drmoratorius/steampack/docs/pics/steampack-01.jpg

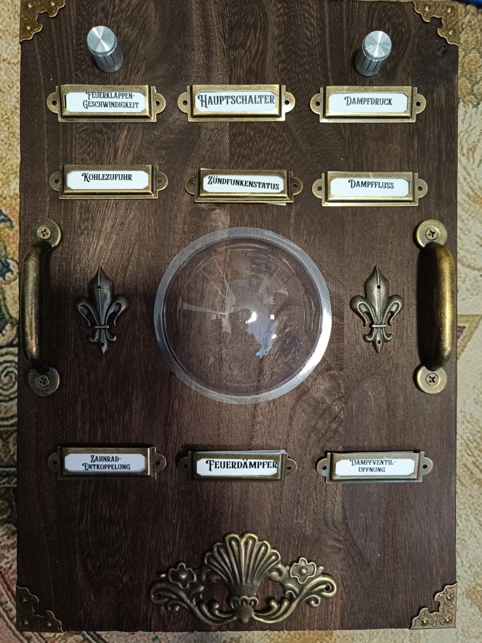
docs/pics/steampack-01.jpg
