drmoratorius/steampack/docs/pics/steampack-02.jpg

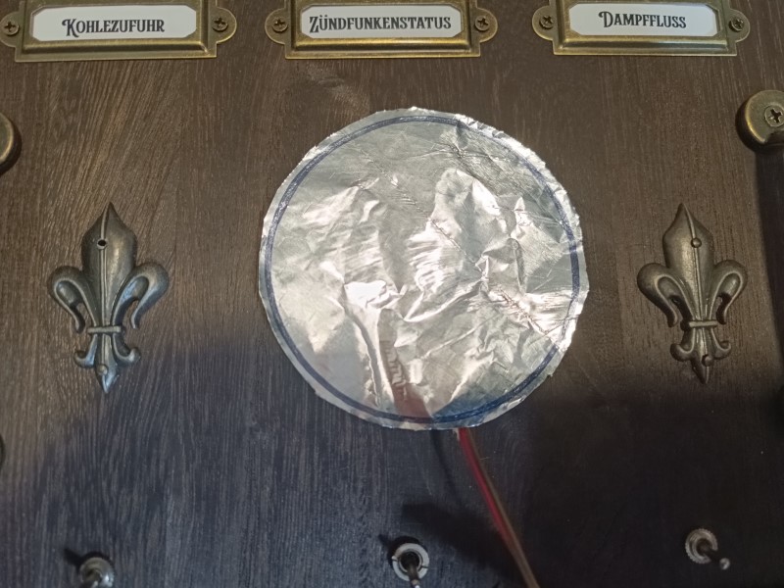
docs/pics/steampack-02.jpg
