drmoratorius/steampack/docs/pics/steampack-13.jpg

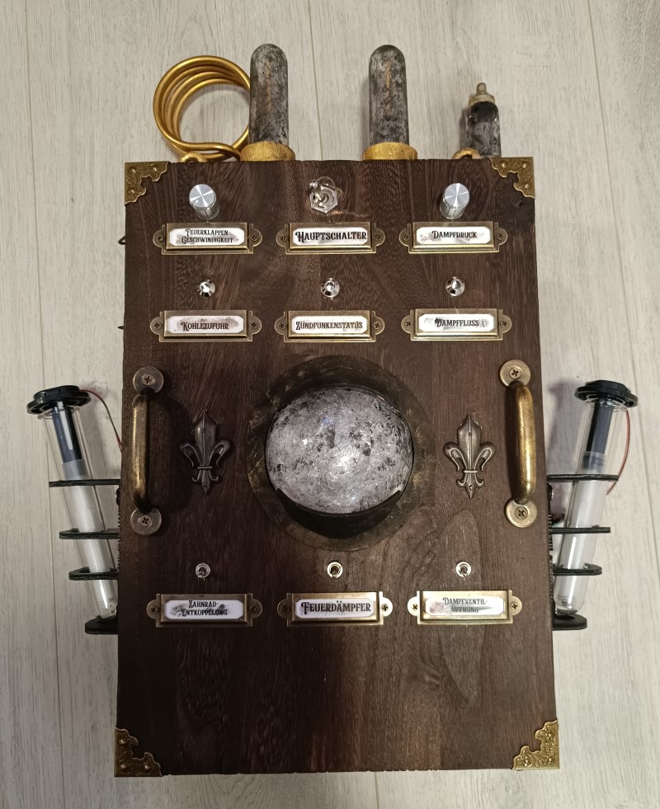
docs/pics/steampack-13.jpg
