drmoratorius/steampack/docs/pics/steampack-15.jpg

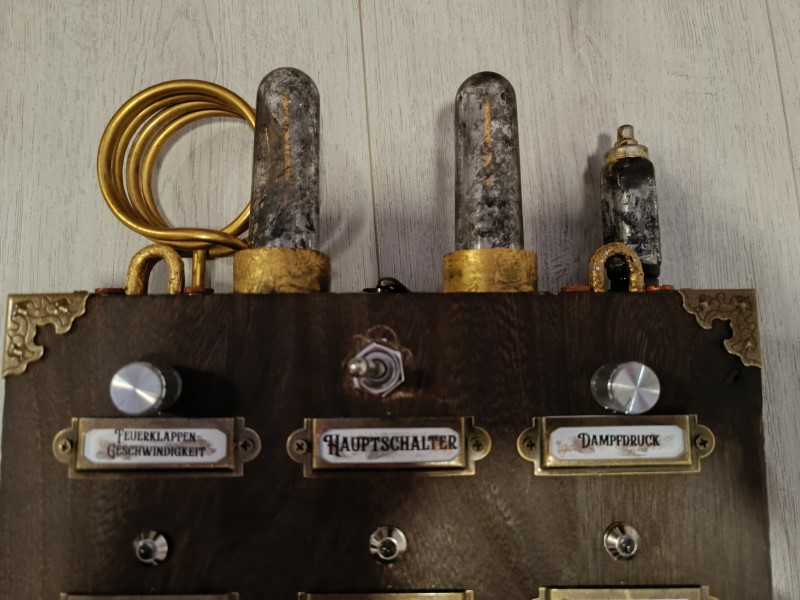
docs/pics/steampack-15.jpg
