drmoratorius/steampack/docs/pics/steampack-final-07.jpg

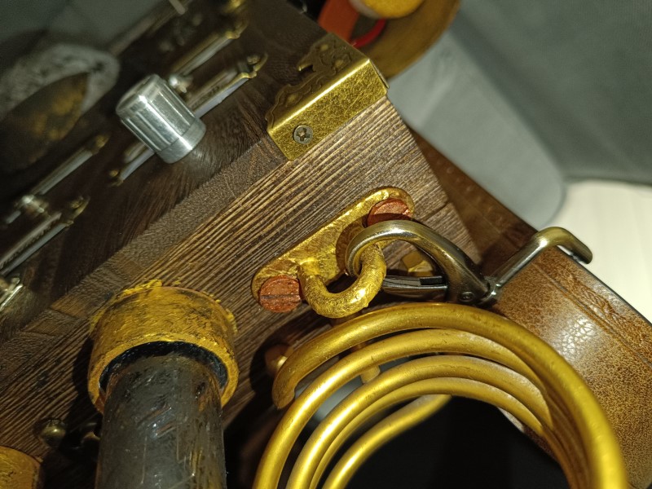
docs/pics/steampack-final-07.jpg
