drmoratorius/steampack/docs/pics/steampack-final-12.jpg

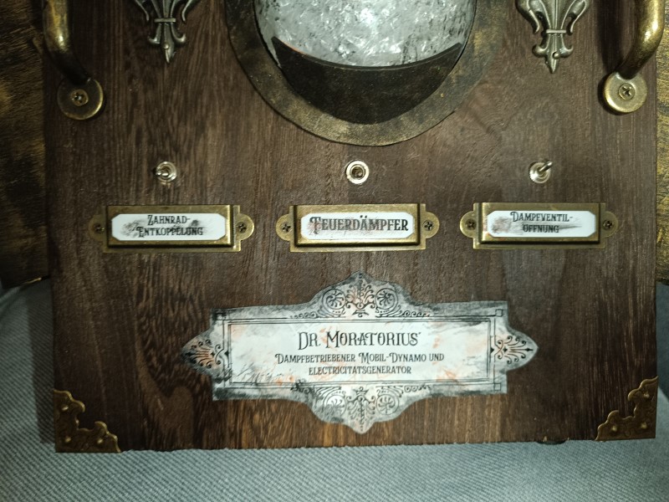
docs/pics/steampack-final-12.jpg
